Peppson/DENNA/src/01_solar_self_watering_plant/node_program.h

#pragma once
#include "../global_config.h"
#include "rf24_radio.h"
#include "hardware.h"
#include "water_system.h"

namespace selected_node {


bool send_data_set_time(RF24Radio& radio, const uint16_t water_level, const uint16_t battery_charge) {
    if (radio.send_message(0, water_level, battery_charge, 0xFFFF) &&
        radio.wait_for_message(3000) &&
        Hardware::set_time_until_deepsleep(radio.message.data_2)) {
        return true;
    }
    
    return false;
}


void send_sensor_data(RF24Radio& radio, const bool request_time) {
    WDT_FEED();

    // Grab sensor data
    radio.power_down();
    uint16_t water_level = WaterSystem::get_water_level();
    uint16_t battery_charge = Hardware::get_remaining_battery_charge();
    radio.power_up();

    // Request current time
    if (request_time) {
        if (send_data_set_time(radio, water_level, battery_charge)) {
            Hardware::next_update_time = millis() + NODE_UPDATE_INTERVAL;
            return;
        }
        // Failure
        Hardware::deepsleep(15*60);
    } 

    // Data update
    radio.send_message(0, water_level, battery_charge, 0);
    Hardware::next_update_time = millis() + NODE_UPDATE_INTERVAL; 
}


void handle_RX_message(RF24Radio& radio) {
    WDT_FEED();

    // Run pump
    if (radio.message.state) {
        radio.stopListening();
        WaterSystem::run_water_pump(radio.message.data_0, IS_PUMP_BATTERY_DRIVEN);
    
    // Commands
    } else switch (radio.message.data_2) {
        case REBOOT: // 0xFFFF
            Hardware::restart_device();
            break;
        case RESEND: // 0xFFFE
            selected_node::send_sensor_data(radio, false);
            break;
        case SLEEP: // 0xFFFD
            Hardware::deepsleep(15*60);
            break;
        default:
            break;
    }

    // Flush buffers in case we recieved another message before "radio.stopListening()"
    if (radio.available()) { 
        radio.flush_rx(); 
    }
}
} // namespace selected_node
