Peppson/DENNA/shared_libs/utility/utility.cpp

#include "utility.h"
#include "hardware.h"
#include "water_system.h"
#include "memory.h"


namespace util {


// Timer function. Call before and after measured code
void benchmark(const char* name) {
    static bool begin_timer = true;
    static uint32_t start_time = 0;

    // Start timer
	if (begin_timer) {
        begin_timer = false;
		start_time = micros();
        return;
	}
    
    // Stop timer + output
    uint32_t end_time = micros() - start_time;
    String num_str = String(end_time);

    // Name (if any)
    if (name != nullptr) { log("%s: ", name); }
    
    // Microseconds
    if (num_str.length() < 4) {
        log("%iμs \n", end_time);

    // Milliseconds
    } else if (num_str.length() < 6) {
        float end_ms = (float)end_time / 1000;
        log("%.3fms \n", end_ms);
    } else {
        log("%ims \n", end_time / 1000);
    }

    // Reset
    begin_timer = true;
    start_time = 0;	
}


// Attinys can only print upto int16_t, this is some kind of workaround for larger nums
void print_int_hack(const uint32_t& value) {
    #if USB_SERIAL_ENABLED
        char buffer[20];
        sprintf(buffer, "%lu", value);
        log("%s\n", buffer);
        delay(20);
    #endif
}


void calibration() {
    WDT_DISABLE(); 
    #if !USB_SERIAL_ENABLED && CALIBRATION
        #error "--- Enable USB_SERIAL_ENABLED in \"global_config.h\" for util::calibration() ---"
    #endif

    #if DEBUG_LOOP_ENABLED
        log("DEBUG_LOOP_ENABLED\n"); 
        debug_loop();
    #elif defined(COFFEE_COUNT)
        log("COFFEE_COUNT\n");
        set_mocca_master_coffee_count();
    #elif ADC_CAL_ENABLED
        log("ADC_CAL_ENABLED\n");
        adc_calibration();
    #elif PUMP_CAL_ENABLED
        log("PUMP_CAL_ENABLED\n"); 
        water_level_calibration();
    #elif SERVO_CAL_ENABLED
        log("SERVO_CAL_ENABLED\n");
        servo_calibration();
    #endif
}


#if ADC_CAL_ENABLED
void adc_calibration() { 
    ADC0.CTRLA |= ADC_ENABLE_bm; // Enable ADC
    log("GOOOO!!!\n");

    while (1) {
        uint32_t sum = 0;
        for (size_t i = 0; i < 100; i++) {
            uint16_t voltage = analogRead(PIN_PA6); 
            sum += constrain(voltage, 0, 1023);
            delay(1); 
        }
        
        uint16_t average = sum / 100;           
        log("Avg: %i\n", average);
        delay(300);
    }
}
#endif


#if PUMP_CAL_ENABLED
void water_level_calibration() {
    //pinMode(PIN_POWER_IO, OUTPUT);
    //digitalWrite(PIN_POWER_IO, LOW); // Pump on/off
    
    while (1) {
        uint32_t level = WaterSystem::get_water_level();
        uint32_t percent = map(level, selected_node::WATER_SENSOR_MIN_VALUE, selected_node::WATER_SENSOR_MAX_VALUE, 0, 100);
        log("Avg: "); print_int_hack(level); log("\n");
        log("Mapped: %i\n", percent);
        delay(500); 
    }
}
#endif


#if SERVO_CAL_ENABLED
void servo_calibration() {
    extern RF24Radio radio;
    uint8_t PIN_SERVO = PIN_PA4;
    radio.begin();
    radio.power_up();
    log("GOOOOO!\n");

    /* 
    ON = 550,
    OFF = 1300,
    MIDDLE_ON = 800,
    MIDDLE_OFF = 950
    */

    while (1) { 
        if (radio.wait_for_message(500)) {
            uint16_t high_pulse = constrain(radio.message.data_2, 0, 2000);
            uint16_t low_pulse = 20*1000 - high_pulse;
            log("Servo pos: %i\n", high_pulse);

            for (uint8_t i = 0; i < 20; i++) {
                digitalWrite(PIN_SERVO, HIGH); 
                delayMicroseconds(high_pulse); 
                digitalWrite(PIN_SERVO, LOW); 
                delayMicroseconds(low_pulse); 
            }
        }       
    }   
} 
#endif


#if defined(COFFEE_COUNT)
void set_mocca_master_coffee_count() {
    log("Overwriting coffee_count to %i...\n", COFFEE_COUNT);

    Memory memory;
    memory.init_raid_variable(COFFEE_COUNT);
    memory.write_raid_variable(COFFEE_COUNT);
    log("coffee_count set to: %i\n", memory.get_raid_variable());
    memory.~Memory();

    log("---- Awaiting reupload ---- \n");
    while (1) {
        delay(2000);
    }
}
#endif


#if DEBUG_LOOP_ENABLED
void debug_loop() {
    uint16_t yep = 123;
    uint16_t* ptr = &yep;
    log("size yep: %i\n", sizeof(yep));
    log("size ptr: %i\n", sizeof(ptr));
    log("value ptr: %i\n", *ptr);

    while (1) {
        delay(1000);
    }
}
#endif


/* 
void button_halt_CPU() {
    pinMode(PIN_PA4, INPUT_PULLUP);
    pinMode(PIN_UPDI, INPUT_PULLUP);

    if (digitalRead(PIN_PA4) == LOW) {
        log("CPU halt!\n");
        while (1) {
            delay(1000);
        }
    }
} 
*/

} // Namepsace util
